arthuralee/tether/poster/IMG_2028.JPG

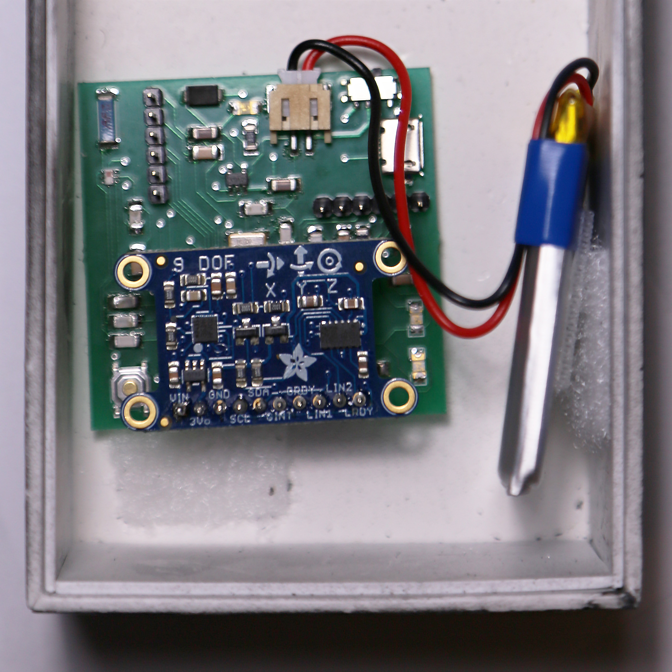
poster/IMG_2028.JPG
